vives-project-xp/GreenhouseSensoring/Code/greenhouse_sensoring/include/sensor.h

#include <Arduino.h>
#ifndef HA_SENSOR_H
#define HA_SENSOR_H


enum class SensorType {
    TEMPERATURE,
    HUMIDITY,
    LIGHT,
    CO2,
    SOIL_MOISTURE,
    PH,
    EC,
    PRESSURE,
    AIRFLOW,
    UV,
    WATERLEVEL,
    BATTERYLEVEL,
    NITROGEN,
    PHOSPHORUS,
    POTASSIUM
};


class HaSensor {

private:
    String name;
    SensorType type;
    String unit;
    float value;
    int min;
    int max;
    String typeToString(SensorType type);


public:
    HaSensor();
    HaSensor(String name, SensorType type, int min, int max);
    void setValue(float value);
        String toJson();
        int getValue();
        int getMax();
};


#endif
